poetaster/spires/Spires-onevoice/scales.h

/* scales generated in supercolider
 * Scale.directory; (36,50,
 * Scale.bhairav.ratios *  80.midicps; (36,48,60,72. ....)
 * does not account for alt tuning, etc.
 * a = Scale.neapolitanMinor.ratios ;///* [36,48,60,72,84].midicps ; 
 * [36,48,60,72,84].do ( { |midi| (midi.midicps * a).postln }) ; will produce all
)
 */
 
// Bank 1 ragas

//nahawand raga up and down
const float Nahawand[28] PROGMEM = {
  65.40639132515, 73.416191979318, 77.781745930466, 87.30705785815, 97.998858995279, 103.82617439479, 123.47082531372, 
  116.54094037925, 130.8127826503, 146.83238395864, 155.56349186093, 174.6141157163, 195.99771799056, 207.65234878959, 
  246.94165062743, 233.08188075851, 261.6255653006, 293.66476791727, 311.12698372187, 349.2282314326, 391.99543598112,  
  415.30469757918, 493.88330125487, 466.16376151701, 523.2511306012, 587.32953583454, 622.25396744373, 698.4564628652,
};

//nahawand raga up and down
const float Bayati[28] PROGMEM = {
65.40639132515, 71.326175505781, 77.781745930466, 87.30705785815, 97.998858995279, 103.82617439479, 116.54094037925,
130.8127826503, 142.65235101156, 155.56349186093, 174.6141157163, 195.99771799056, 207.65234878959, 233.08188075851,
261.6255653006, 285.30470202312, 311.12698372187, 349.2282314326, 391.99543598112, 415.30469757918, 466.16376151701,
523.2511306012, 570.60940404625, 622.25396744373, 698.4564628652, 783.99087196223, 830.60939515835, 932.32752303403,
};


const float NawaAthar[32] PROGMEM = {
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
[ 261.6255653006, 277.18263097681, 311.12698372187, 349.2282314326, 391.99543598112, 415.30469757918, 466.16376151701 ]
[ 523.2511306012, 554.36526195362, 622.25396744373, 698.4564628652, 783.99087196223, 830.60939515835, 932.32752303403 ]
*/
